PorcoMaster/VoronTower/Voron Tower/Files/Stl/Z Bearing/front_idler_bottom_b_1.stl

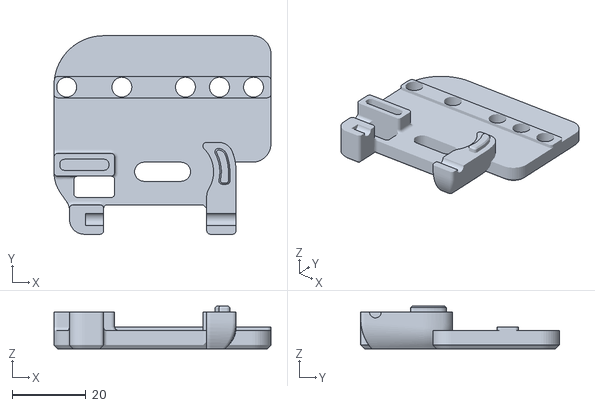
[picture p22: CAD file, 2024-04-04]
Voron Tower/Files/Stl/Z Bearing/front_idler_bottom_b_1.stl
59.0 x 54.0 x 11.6
