PorcoMaster/VoronTower/Voron Tower/Files/Stl/Z Belt Driver for 4040/z_belt_driver_b_2.stl

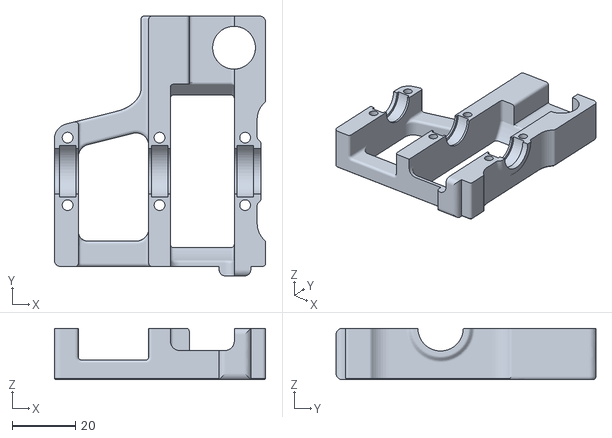
[picture p23: CAD file, 2024-04-04]
Voron Tower/Files/Stl/Z Belt Driver for 4040/z_belt_driver_b_2.stl
66.7 x 82.0 x 16.2
