PorcoMaster/VoronTower/Voron Tower/Files/Stl/Z idler 4040/z_idler_4040_1_b.stl

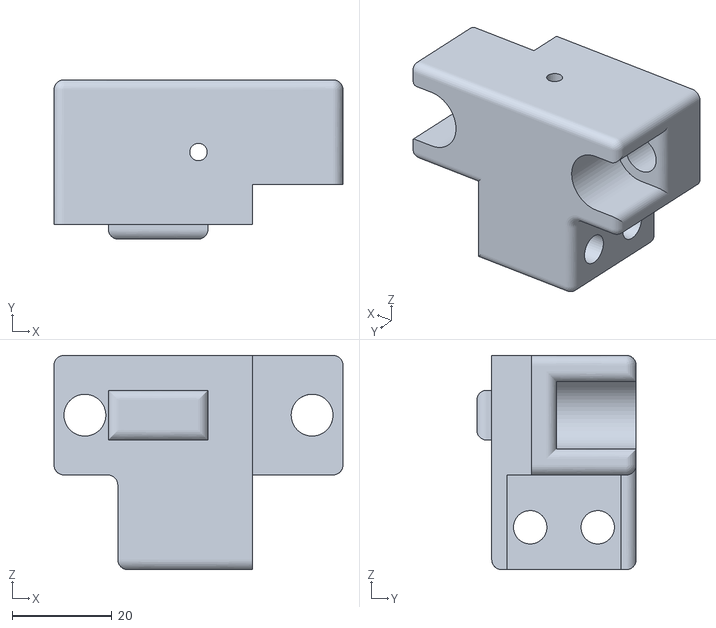
[picture p24: CAD file, 2024-04-04]
Voron Tower/Files/Stl/Z idler 4040/z_idler_4040_1_b.stl
58.0 x 32.0 x 43.0
