PorcoMaster/VoronTower/Voron Tower/Files/Stl/A B Drive/b_drive_2.stl

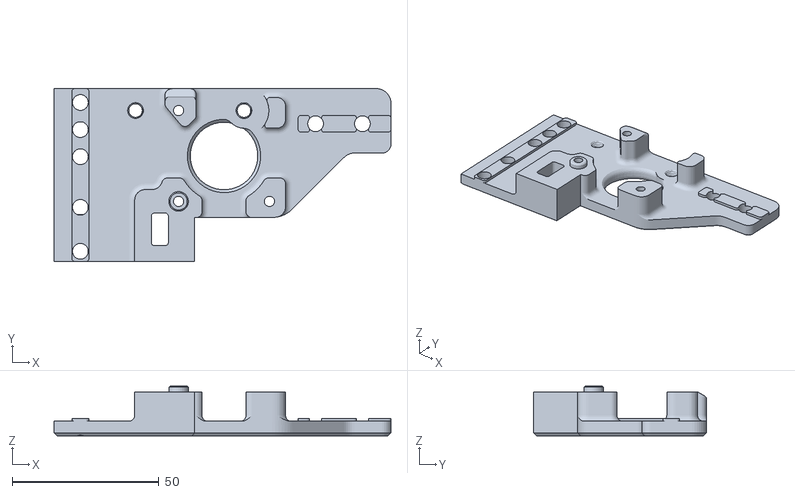
[picture p25: CAD file, 2024-04-04]
Voron Tower/Files/Stl/A B Drive/b_drive_2.stl
115.0 x 59.0 x 17.0
