PorcoMaster/VoronTower/Voron Tower/Files/Stl/Z Bearing/z_belt_clamp.stl

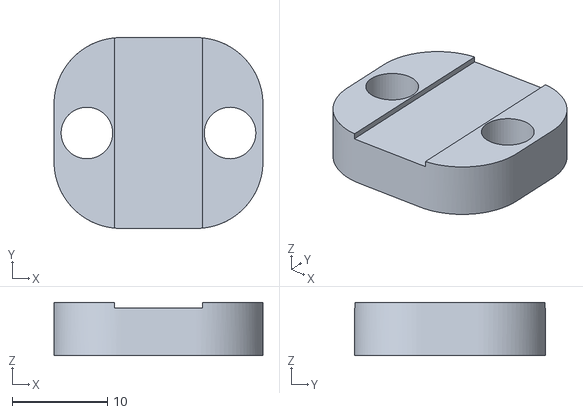
[picture p26: CAD file, 2024-04-04]
Voron Tower/Files/Stl/Z Bearing/z_belt_clamp.stl
21.9 x 20.0 x 5.60
