PorcoMaster/VoronTower/Voron Tower/Files/Stl/Z Belt Driver for 4040/belt_tensioner_a.stl

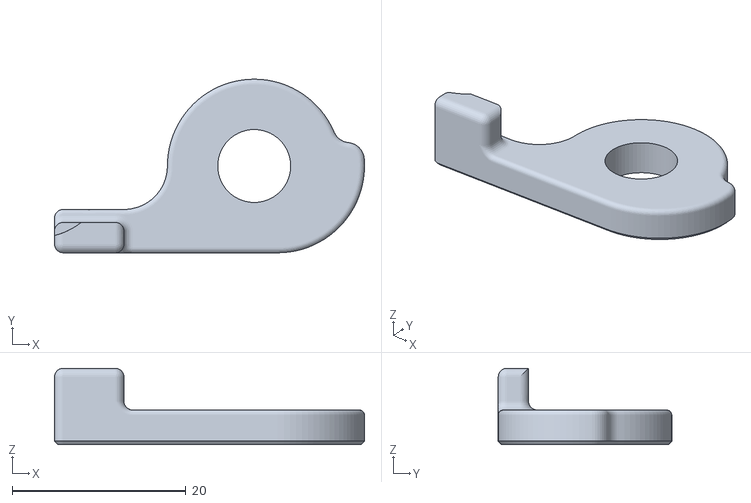
[picture p27: CAD file, 2024-04-04]
Voron Tower/Files/Stl/Z Belt Driver for 4040/belt_tensioner_a.stl
35.7 x 20.0 x 8.80
