PorcoMaster/VoronTower/Voron Tower/Files/Stl/Door Clips/door_hinge.stl

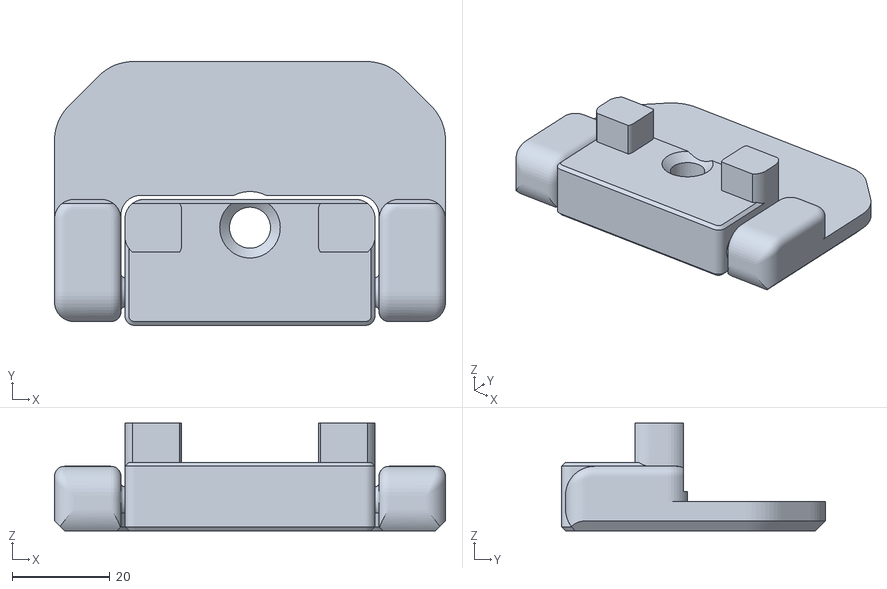
[picture p28: CAD file, 2024-04-04]
Voron Tower/Files/Stl/Door Clips/door_hinge.stl
80.0 x 54.0 x 22.0
