PorcoMaster/VoronTower/Voron Tower/Files/Stl/Door Clips/door_latch.stl

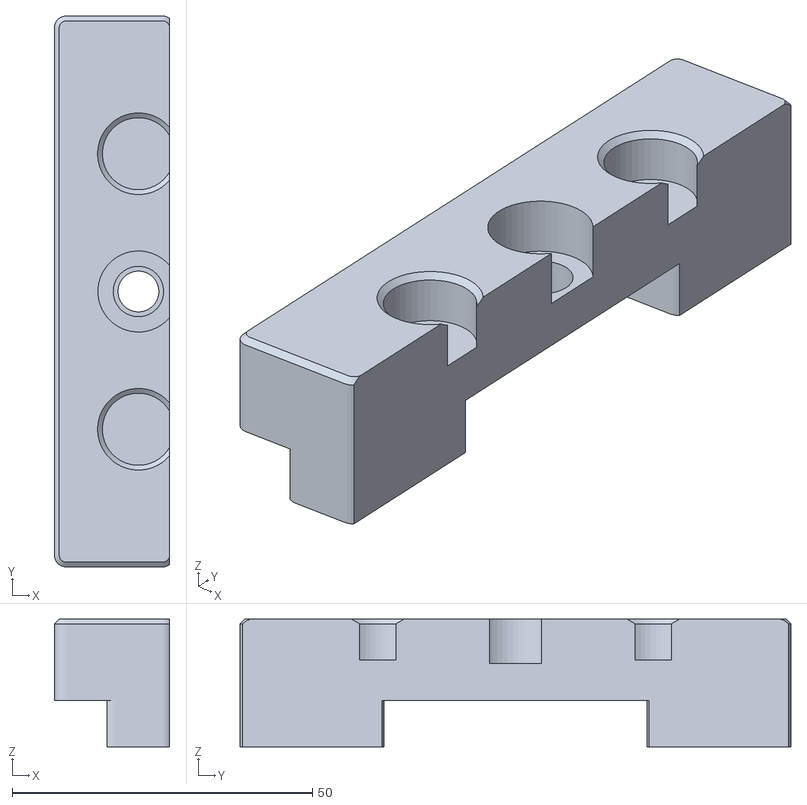
[picture p29: CAD file, 2024-04-04]
Voron Tower/Files/Stl/Door Clips/door_latch.stl
19.2 x 91.7 x 21.3
