PorcoMaster/VoronTower/Voron Tower/Files/Stl/Door Clips/door_handle_b.stl

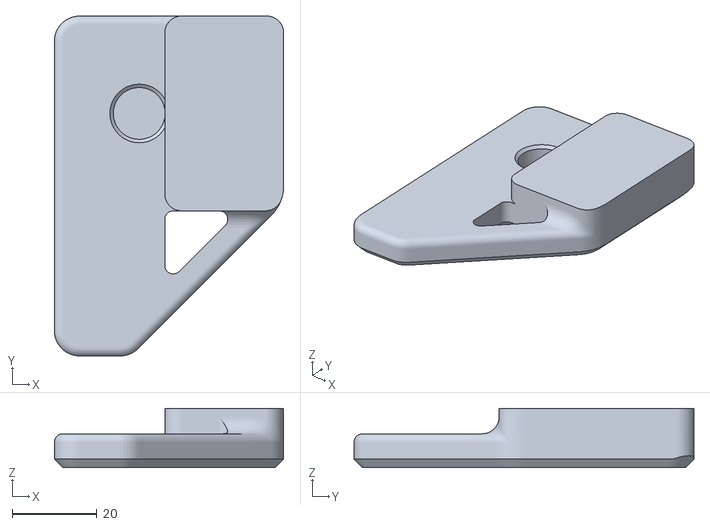
[picture p30: CAD file, 2024-04-04]
Voron Tower/Files/Stl/Door Clips/door_handle_b.stl
54.0 x 80.0 x 14.0
